reality2-ai/r2-3dprint/xiao/src/mariko_logo_traced.scad

// Mariko tree logo, auto-traced from the supplied logo image.
// Source bitmap 254x281px. Even-odd fill: holes are separate paths.
mariko_logo_px_w = 254;
mariko_logo_px_h = 281;
mariko_logo_pts = [
  [3.0,-140.0],
  [-16.0,-139.0],
  [-17.0,-138.0],
  [-22.0,-138.0],
  [-23.0,-137.0],
  [-31.0,-136.0],
  [-48.0,-130.0],
  [-69.0,-118.0],
  [-78.0,-111.0],
  [-94.5,-94.5],
  [-101.5,-85.5],
  [-108.5,-74.5],
  [-119.5,-50.5],
  [-119.5,-47.5],
  [-115.0,-44.0],
  [-43.0,-44.0],
  [-42.0,-43.0],
  [-36.0,-43.0],
  [-26.0,-40.0],
  [-21.5,-36.5],
  [-17.5,-29.5],
  [-17.5,-17.5],
  [-22.5,-8.5],
  [-30.0,-2.0],
  [-38.0,3.0],
  [-54.0,8.0],
  [-70.0,9.0],
  [-71.0,8.0],
  [-86.0,6.0],
  [-87.0,5.0],
  [-106.0,5.0],
  [-110.0,1.0],
  [-114.0,-1.0],
  [-121.0,0.0],
  [-124.5,2.5],
  [-127.5,7.5],
  [-127.5,13.5],
  [-125.5,17.5],
  [-119.0,22.0],
  [-113.0,22.0],
  [-109.0,20.0],
  [-106.5,17.5],
  [-104.0,11.0],
  [-101.0,12.0],
  [-83.0,13.0],
  [-78.5,14.5],
  [-95.0,26.0],
  [-104.0,35.0],
  [-112.0,34.0],
  [-116.0,36.0],
  [-119.5,39.5],
  [-120.5,41.5],
  [-120.5,49.5],
  [-118.5,52.5],
  [-112.0,57.0],
  [-107.0,57.0],
  [-104.0,56.0],
  [-99.5,51.5],
  [-97.5,46.5],
  [-99.5,39.5],
  [-94.0,34.0],
  [-78.0,23.0],
  [-65.0,18.0],
  [-64.5,19.5],
  [-68.5,24.5],
  [-70.5,29.5],
  [-72.0,31.0],
  [-76.0,31.0],
  [-80.0,33.0],
  [-83.5,38.5],
  [-83.5,45.5],
  [-81.0,50.0],
  [-76.0,53.0],
  [-68.0,53.0],
  [-64.5,50.5],
  [-61.5,46.5],
  [-60.5,41.5],
  [-61.5,40.5],
  [-61.5,37.5],
  [-64.5,33.5],
  [-64.5,31.5],
  [-59.5,24.5],
  [-51.0,17.0],
  [-26.0,6.0],
  [-12.5,-3.5],
  [-12.5,0.5],
  [-14.5,5.5],
  [-33.0,24.0],
  [-41.0,23.0],
  [-45.0,25.0],
  [-49.5,30.5],
  [-49.5,38.5],
  [-44.0,45.0],
  [-41.0,46.0],
  [-33.0,45.0],
  [-27.5,38.5],
  [-27.5,35.5],
  [-26.5,34.5],
  [-28.5,29.5],
  [-10.0,12.0],
  [-8.5,14.5],
  [-8.5,21.5],
  [-10.5,28.5],
  [-16.5,38.5],
  [-26.0,48.0],
  [-38.0,54.0],
  [-46.0,55.0],
  [-47.0,56.0],
  [-53.0,56.0],
  [-54.0,57.0],
  [-62.0,57.0],
  [-63.0,58.0],
  [-67.0,58.0],
  [-73.0,60.0],
  [-86.0,68.0],
  [-93.0,66.0],
  [-98.0,67.0],
  [-101.5,69.5],
  [-104.5,73.5],
  [-104.5,81.5],
  [-99.0,88.0],
  [-97.0,89.0],
  [-90.0,89.0],
  [-83.5,83.5],
  [-82.5,81.5],
  [-82.5,73.5],
  [-78.0,70.0],
  [-63.0,64.0],
  [-50.0,63.0],
  [-60.5,77.5],
  [-68.5,94.5],
  [-72.0,95.0],
  [-75.0,97.0],
  [-78.5,101.5],
  [-78.5,110.5],
  [-76.5,113.5],
  [-71.0,117.0],
  [-64.0,117.0],
  [-59.5,114.5],
  [-56.5,109.5],
  [-56.5,101.5],
  [-58.5,98.5],
  [-61.5,96.5],
  [-60.5,91.5],
  [-51.5,76.5],
  [-37.0,63.0],
  [-36.0,63.0],
  [-35.5,64.5],
  [-38.5,71.5],
  [-38.5,76.5],
  [-40.0,79.0],
  [-43.0,80.0],
  [-46.5,83.5],
  [-47.5,85.5],
  [-47.5,93.5],
  [-42.0,100.0],
  [-39.0,101.0],
  [-33.0,101.0],
  [-26.5,95.5],
  [-24.5,90.5],
  [-25.5,85.5],
  [-27.5,82.5],
  [-32.5,78.5],
  [-31.5,77.5],
  [-29.5,67.5],
  [-25.5,59.5],
  [-12.0,46.0],
  [-8.0,44.0],
  [-6.5,45.5],
  [-6.5,51.5],
  [-5.5,52.5],
  [-5.5,77.5],
  [-7.5,83.5],
  [-13.5,93.5],
  [-33.0,113.0],
  [-34.0,112.0],
  [-40.0,112.0],
  [-46.5,116.5],
  [-48.5,120.5],
  [-48.5,125.5],
  [-46.5,129.5],
  [-43.0,133.0],
  [-38.0,135.0],
  [-32.0,134.0],
  [-25.5,126.5],
  [-26.5,116.5],
  [-6.0,96.0],
  [-4.5,98.5],
  [-4.5,118.5],
  [-7.0,120.0],
  [-11.5,125.5],
  [-11.5,133.5],
  [-6.0,140.0],
  [-3.0,141.0],
  [5.0,140.0],
  [9.5,135.5],
  [11.5,130.5],
  [9.5,123.5],
  [3.5,118.5],
  [3.5,102.5],
  [4.5,101.5],
  [5.0,96.0],
  [26.5,117.5],
  [24.5,120.5],
  [24.5,125.5],
  [25.5,128.5],
  [30.0,133.0],
  [35.0,135.0],
  [41.0,134.0],
  [47.5,126.5],
  [47.5,120.5],
  [45.5,116.5],
  [42.0,113.0],
  [39.0,112.0],
  [33.0,112.0],
  [32.0,113.0],
  [13.5,94.5],
  [5.5,80.5],
  [5.5,77.5],
  [4.5,76.5],
  [4.5,54.5],
  [5.5,53.5],
  [5.5,47.5],
  [7.0,44.0],
  [10.0,45.0],
  [25.5,60.5],
  [27.5,64.5],
  [31.5,78.5],
  [29.0,80.0],
  [24.5,85.5],
  [24.5,93.5],
  [25.5,95.5],
  [32.0,101.0],
  [39.0,101.0],
  [41.0,100.0],
  [46.5,93.5],
  [46.5,85.5],
  [45.5,83.5],
  [42.0,80.0],
  [38.5,78.5],
  [36.5,67.5],
  [34.5,64.5],
  [35.0,63.0],
  [36.0,63.0],
  [51.5,77.5],
  [55.5,83.5],
  [60.5,93.5],
  [60.5,96.5],
  [55.5,102.5],
  [55.5,109.5],
  [56.5,111.5],
  [63.0,117.0],
  [71.0,117.0],
  [74.0,115.0],
  [77.5,110.5],
  [78.5,104.5],
  [76.5,99.5],
  [73.0,96.0],
  [67.5,94.5],
  [61.5,80.5],
  [49.0,63.0],
  [62.0,64.0],
  [69.0,66.0],
  [77.0,70.0],
  [81.5,73.5],
  [81.5,81.5],
  [82.5,83.5],
  [89.0,89.0],
  [96.0,89.0],
  [101.0,86.0],
  [103.5,82.5],
  [103.5,78.5],
  [104.5,77.5],
  [102.5,71.5],
  [97.0,67.0],
  [92.0,66.0],
  [85.0,68.0],
  [70.0,59.0],
  [37.0,54.0],
  [28.0,50.0],
  [24.0,47.0],
  [16.5,39.5],
  [10.5,30.5],
  [8.5,24.5],
  [8.5,20.5],
  [7.5,19.5],
  [7.5,15.5],
  [9.0,12.0],
  [27.5,29.5],
  [26.5,30.5],
  [26.5,38.5],
  [31.0,44.0],
  [35.0,46.0],
  [43.0,45.0],
  [47.5,40.5],
  [48.5,38.5],
  [48.5,30.5],
  [44.0,25.0],
  [40.0,23.0],
  [32.0,24.0],
  [14.5,6.5],
  [12.5,3.5],
  [12.0,-3.0],
  [27.0,7.0],
  [40.0,13.0],
  [42.0,13.0],
  [50.0,17.0],
  [55.0,21.0],
  [63.5,31.5],
  [63.5,33.5],
  [60.5,38.5],
  [60.5,45.5],
  [61.5,47.5],
  [68.0,53.0],
  [76.0,53.0],
  [80.5,49.5],
  [82.5,46.5],
  [82.5,37.5],
  [79.0,33.0],
  [76.0,31.0],
  [72.0,31.0],
  [69.5,29.5],
  [67.5,24.5],
  [63.5,19.5],
  [64.0,18.0],
  [71.0,20.0],
  [79.0,24.0],
  [92.0,33.0],
  [98.5,39.5],
  [96.5,45.5],
  [98.5,51.5],
  [102.0,55.0],
  [106.0,57.0],
  [111.0,57.0],
  [115.0,55.0],
  [119.5,49.5],
  [119.5,41.5],
  [118.5,39.5],
  [114.0,35.0],
  [111.0,34.0],
  [103.0,35.0],
  [93.0,25.0],
  [77.5,14.5],
  [82.0,14.0],
  [83.0,13.0],
  [89.0,13.0],
  [90.0,12.0],
  [100.0,12.0],
  [103.0,11.0],
  [104.5,12.5],
  [104.5,15.5],
  [106.5,18.5],
  [112.0,22.0],
  [119.0,22.0],
  [121.0,21.0],
  [126.5,14.5],
  [126.5,7.5],
  [124.5,3.5],
  [122.0,1.0],
  [117.0,-1.0],
  [111.0,0.0],
  [105.0,5.0],
  [86.0,5.0],
  [85.0,6.0],
  [80.0,6.0],
  [79.0,7.0],
  [75.0,7.0],
  [69.0,9.0],
  [60.0,9.0],
  [59.0,8.0],
  [48.0,7.0],
  [32.0,0.0],
  [19.5,-11.5],
  [16.5,-17.5],
  [16.5,-28.5],
  [18.5,-33.5],
  [24.0,-39.0],
  [28.0,-41.0],
  [35.0,-43.0],
  [42.0,-43.0],
  [43.0,-44.0],
  [114.0,-44.0],
  [118.5,-47.5],
  [118.5,-50.5],
  [110.5,-69.5],
  [100.5,-85.5],
  [94.5,-93.5],
  [71.0,-116.0],
  [57.0,-125.0],
  [42.0,-132.0],
  [26.0,-137.0],
  [16.0,-138.0],
  [15.0,-139.0],
  [4.0,-139.0],
  [30.5,-118.5],
  [35.0,-118.0],
  [42.0,-115.0],
  [48.5,-108.5],
  [51.5,-101.5],
  [52.0,-93.0],
  [54.0,-95.0],
  [63.0,-99.0],
  [74.0,-99.0],
  [75.0,-98.0],
  [78.0,-98.0],
  [87.0,-93.0],
  [91.5,-88.5],
  [94.5,-83.5],
  [95.5,-76.5],
  [96.5,-75.5],
  [95.5,-68.5],
  [92.5,-61.5],
  [88.5,-56.5],
  [82.0,-52.0],
  [73.0,-50.0],
  [64.0,-53.0],
  [56.5,-60.5],
  [54.5,-65.5],
  [54.5,-71.5],
  [58.5,-79.5],
  [64.0,-84.0],
  [67.0,-85.0],
  [74.0,-85.0],
  [80.5,-80.5],
  [82.5,-76.5],
  [82.5,-73.5],
  [78.0,-67.0],
  [74.0,-66.0],
  [70.5,-68.5],
  [71.0,-70.0],
  [74.0,-70.0],
  [75.5,-72.5],
  [72.0,-77.0],
  [69.0,-77.0],
  [64.5,-72.5],
  [64.5,-65.5],
  [71.0,-60.0],
  [78.0,-60.0],
  [85.5,-66.5],
  [87.5,-71.5],
  [87.5,-77.5],
  [85.5,-82.5],
  [80.0,-88.0],
  [76.0,-90.0],
  [68.0,-91.0],
  [58.0,-88.0],
  [51.5,-81.5],
  [39.5,-64.5],
  [33.0,-58.0],
  [17.0,-48.0],
  [12.0,-44.0],
  [7.5,-38.5],
  [6.5,-31.5],
  [5.5,-30.5],
  [5.5,-25.5],
  [4.5,-24.5],
  [3.5,-13.5],
  [0.0,-9.0],
  [-1.0,-9.0],
  [-4.5,-13.5],
  [-7.5,-36.5],
  [-10.5,-41.5],
  [-18.0,-48.0],
  [-34.0,-58.0],
  [-40.5,-64.5],
  [-50.5,-79.5],
  [-59.0,-88.0],
  [-69.0,-91.0],
  [-77.0,-90.0],
  [-81.0,-88.0],
  [-86.5,-82.5],
  [-88.5,-76.5],
  [-87.5,-69.5],
  [-85.5,-65.5],
  [-81.5,-61.5],
  [-78.0,-60.0],
  [-72.0,-60.0],
  [-70.0,-61.0],
  [-64.5,-67.5],
  [-66.5,-74.5],
  [-70.0,-77.0],
  [-73.0,-77.0],
  [-75.5,-74.5],
  [-75.5,-71.5],
  [-74.0,-70.0],
  [-72.0,-70.0],
  [-71.5,-68.5],
  [-76.0,-66.0],
  [-81.5,-69.5],
  [-82.5,-71.5],
  [-82.5,-78.5],
  [-75.0,-85.0],
  [-67.0,-85.0],
  [-62.0,-82.0],
  [-58.5,-78.5],
  [-55.5,-72.5],
  [-55.5,-64.5],
  [-59.5,-57.5],
  [-65.0,-53.0],
  [-74.0,-50.0],
  [-83.0,-52.0],
  [-86.0,-54.0],
  [-94.5,-63.5],
  [-96.5,-69.5],
  [-96.5,-79.5],
  [-93.5,-86.5],
  [-88.0,-93.0],
  [-75.0,-99.0],
  [-64.0,-99.0],
  [-55.0,-95.0],
  [-53.0,-93.0],
  [-51.5,-104.5],
  [-48.0,-110.0],
  [-44.0,-114.0],
  [-39.0,-117.0],
  [-27.0,-119.0],
  [-17.0,-116.0],
  [-8.5,-108.5],
  [-5.5,-101.5],
  [-5.5,-94.5],
  [-9.5,-86.5],
  [-14.0,-82.0],
  [-23.0,-79.0],
  [-32.0,-81.0],
  [-36.5,-84.5],
  [-39.5,-89.5],
  [-39.5,-97.5],
  [-37.5,-101.5],
  [-32.0,-105.0],
  [-28.0,-105.0],
  [-23.5,-102.5],
  [-22.5,-100.5],
  [-23.0,-96.0],
  [-26.0,-98.0],
  [-30.0,-98.0],
  [-31.5,-95.5],
  [-31.5,-92.5],
  [-28.0,-89.0],
  [-25.0,-88.0],
  [-20.0,-89.0],
  [-17.5,-91.5],
  [-15.5,-95.5],
  [-15.5,-101.5],
  [-21.0,-108.0],
  [-25.0,-110.0],
  [-32.0,-110.0],
  [-37.0,-108.0],
  [-42.5,-102.5],
  [-44.5,-98.5],
  [-44.5,-87.5],
  [-40.5,-76.5],
  [-36.5,-70.5],
  [-31.0,-65.0],
  [-11.0,-51.0],
  [-5.0,-49.0],
  [8.0,-50.0],
  [21.0,-58.0],
  [30.0,-65.0],
  [36.5,-71.5],
  [42.5,-83.5],
  [42.5,-86.5],
  [43.5,-87.5],
  [43.5,-98.5],
  [41.5,-102.5],
  [36.0,-108.0],
  [32.0,-110.0],
  [24.0,-110.0],
  [20.0,-108.0],
  [15.5,-103.5],
  [14.5,-100.5],
  [14.5,-96.5],
  [16.5,-91.5],
  [22.0,-88.0],
  [24.0,-88.0],
  [29.5,-90.5],
  [30.5,-96.5],
  [29.0,-98.0],
  [25.0,-98.0],
  [23.5,-95.5],
  [22.0,-95.0],
  [21.5,-100.5],
  [27.0,-105.0],
  [32.0,-105.0],
  [36.5,-101.5],
  [39.5,-93.5],
  [38.5,-92.5],
  [38.5,-89.5],
  [36.5,-85.5],
  [31.0,-81.0],
  [24.0,-79.0],
  [17.0,-80.0],
  [13.0,-82.0],
  [9.5,-85.5],
  [5.5,-92.5],
  [4.5,-100.5],
  [5.5,-101.5],
  [5.5,-104.5],
  [8.5,-109.5],
  [13.0,-114.0],
  [21.0,-118.0],
  [25.0,-118.0],
  [26.0,-119.0]
];
mariko_logo_paths = [
  [0, 1, 2, 3, 4, 5, 6, 7, 8, 9, 10, 11, 12, 13, 14, 15, 16, 17, 18, 19, 20, 21, 22, 23, 24, 25, 26, 27, 28, 29, 30, 31, 32, 33, 34, 35, 36, 37, 38, 39, 40, 41, 42, 43, 44, 45, 46, 47, 48, 49, 50, 51, 52, 53, 54, 55, 56, 57, 58, 59, 60, 61, 62, 63, 64, 65, 66, 67, 68, 69, 70, 71, 72, 73, 74, 75, 76, 77, 78, 79, 80, 81, 82, 83, 84, 85, 86, 87, 88, 89, 90, 91, 92, 93, 94, 95, 96, 97, 98, 99, 100, 101, 102, 103, 104, 105, 106, 107, 108, 109, 110, 111, 112, 113, 114, 115, 116, 117, 118, 119, 120, 121, 122, 123, 124, 125, 126, 127, 128, 129, 130, 131, 132, 133, 134, 135, 136, 137, 138, 139, 140, 141, 142, 143, 144, 145, 146, 147, 148, 149, 150, 151, 152, 153, 154, 155, 156, 157, 158, 159, 160, 161, 162, 163, 164, 165, 166, 167, 168, 169, 170, 171, 172, 173, 174, 175, 176, 177, 178, 179, 180, 181, 182, 183, 184, 185, 186, 187, 188, 189, 190, 191, 192, 193, 194, 195, 196, 197, 198, 199, 200, 201, 202, 203, 204, 205, 206, 207, 208, 209, 210, 211, 212, 213, 214, 215, 216, 217, 218, 219, 220, 221, 222, 223, 224, 225, 226, 227, 228, 229, 230, 231, 232, 233, 234, 235, 236, 237, 238, 239, 240, 241, 242, 243, 244, 245, 246, 247, 248, 249, 250, 251, 252, 253, 254, 255, 256, 257, 258, 259, 260, 261, 262, 263, 264, 265, 266, 267, 268, 269, 270, 271, 272, 273, 274, 275, 276, 277, 278, 279, 280, 281, 282, 283, 284, 285, 286, 287, 288, 289, 290, 291, 292, 293, 294, 295, 296, 297, 298, 299, 300, 301, 302, 303, 304, 305, 306, 307, 308, 309, 310, 311, 312, 313, 314, 315, 316, 317, 318, 319, 320, 321, 322, 323, 324, 325, 326, 327, 328, 329, 330, 331, 332, 333, 334, 335, 336, 337, 338, 339, 340, 341, 342, 343, 344, 345, 346, 347, 348, 349, 350, 351, 352, 353, 354, 355, 356, 357, 358, 359, 360, 361, 362, 363, 364, 365, 366, 367, 368, 369, 370, 371, 372, 373, 374, 375, 376, 377, 378, 379, 380, 381, 382, 383, 384, 385, 386, 387, 388, 389, 390, 391, 392, 393],
  [394, 395, 396, 397, 398, 399, 400, 401, 402, 403, 404, 405, 406, 407, 408, 409, 410, 411, 412, 413, 414, 415, 416, 417, 418, 419, 420, 421, 422, 423, 424, 425, 426, 427, 428, 429, 430, 431, 432, 433, 434, 435, 436, 437, 438, 439, 440, 441, 442, 443, 444, 445, 446, 447, 448, 449, 450, 451, 452, 453, 454, 455, 456, 457, 458, 459, 460, 461, 462, 463, 464, 465, 466, 467, 468, 469, 470, 471, 472, 473, 474, 475, 476, 477, 478, 479, 480, 481, 482, 483, 484, 485, 486, 487, 488, 489, 490, 491, 492, 493, 494, 495, 496, 497, 498, 499, 500, 501, 502, 503, 504, 505, 506, 507, 508, 509, 510, 511, 512, 513, 514, 515, 516, 517, 518, 519, 520, 521, 522, 523, 524, 525, 526, 527, 528, 529, 530, 531, 532, 533, 534, 535, 536, 537, 538, 539, 540, 541, 542, 543, 544, 545, 546, 547, 548, 549, 550, 551, 552, 553, 554, 555, 556, 557, 558, 559, 560, 561, 562, 563, 564, 565, 566, 567, 568, 569, 570, 571, 572, 573, 574, 575, 576, 577, 578, 579, 580, 581, 582, 583, 584, 585, 586, 587, 588, 589, 590, 591, 592, 593, 594, 595, 596, 597, 598, 599, 600, 601]
];

// the logo, centred on its bitmap centre, scaled to the requested width (mm)
module mariko_logo2d(w=18){
    scale(w/mariko_logo_px_w)
        polygon(points=mariko_logo_pts, paths=mariko_logo_paths);
}
