reality2-ai/r2-3dprint/xiao/test/seated.scad

use <../src/xiao_case.scad>
case_body();
translate([0,0,11.4]) lid();
